id-studiolab/foodSampler/device/hw/foodSampler_v20/_REF/foodSampler_v20_SCHEM.pdf

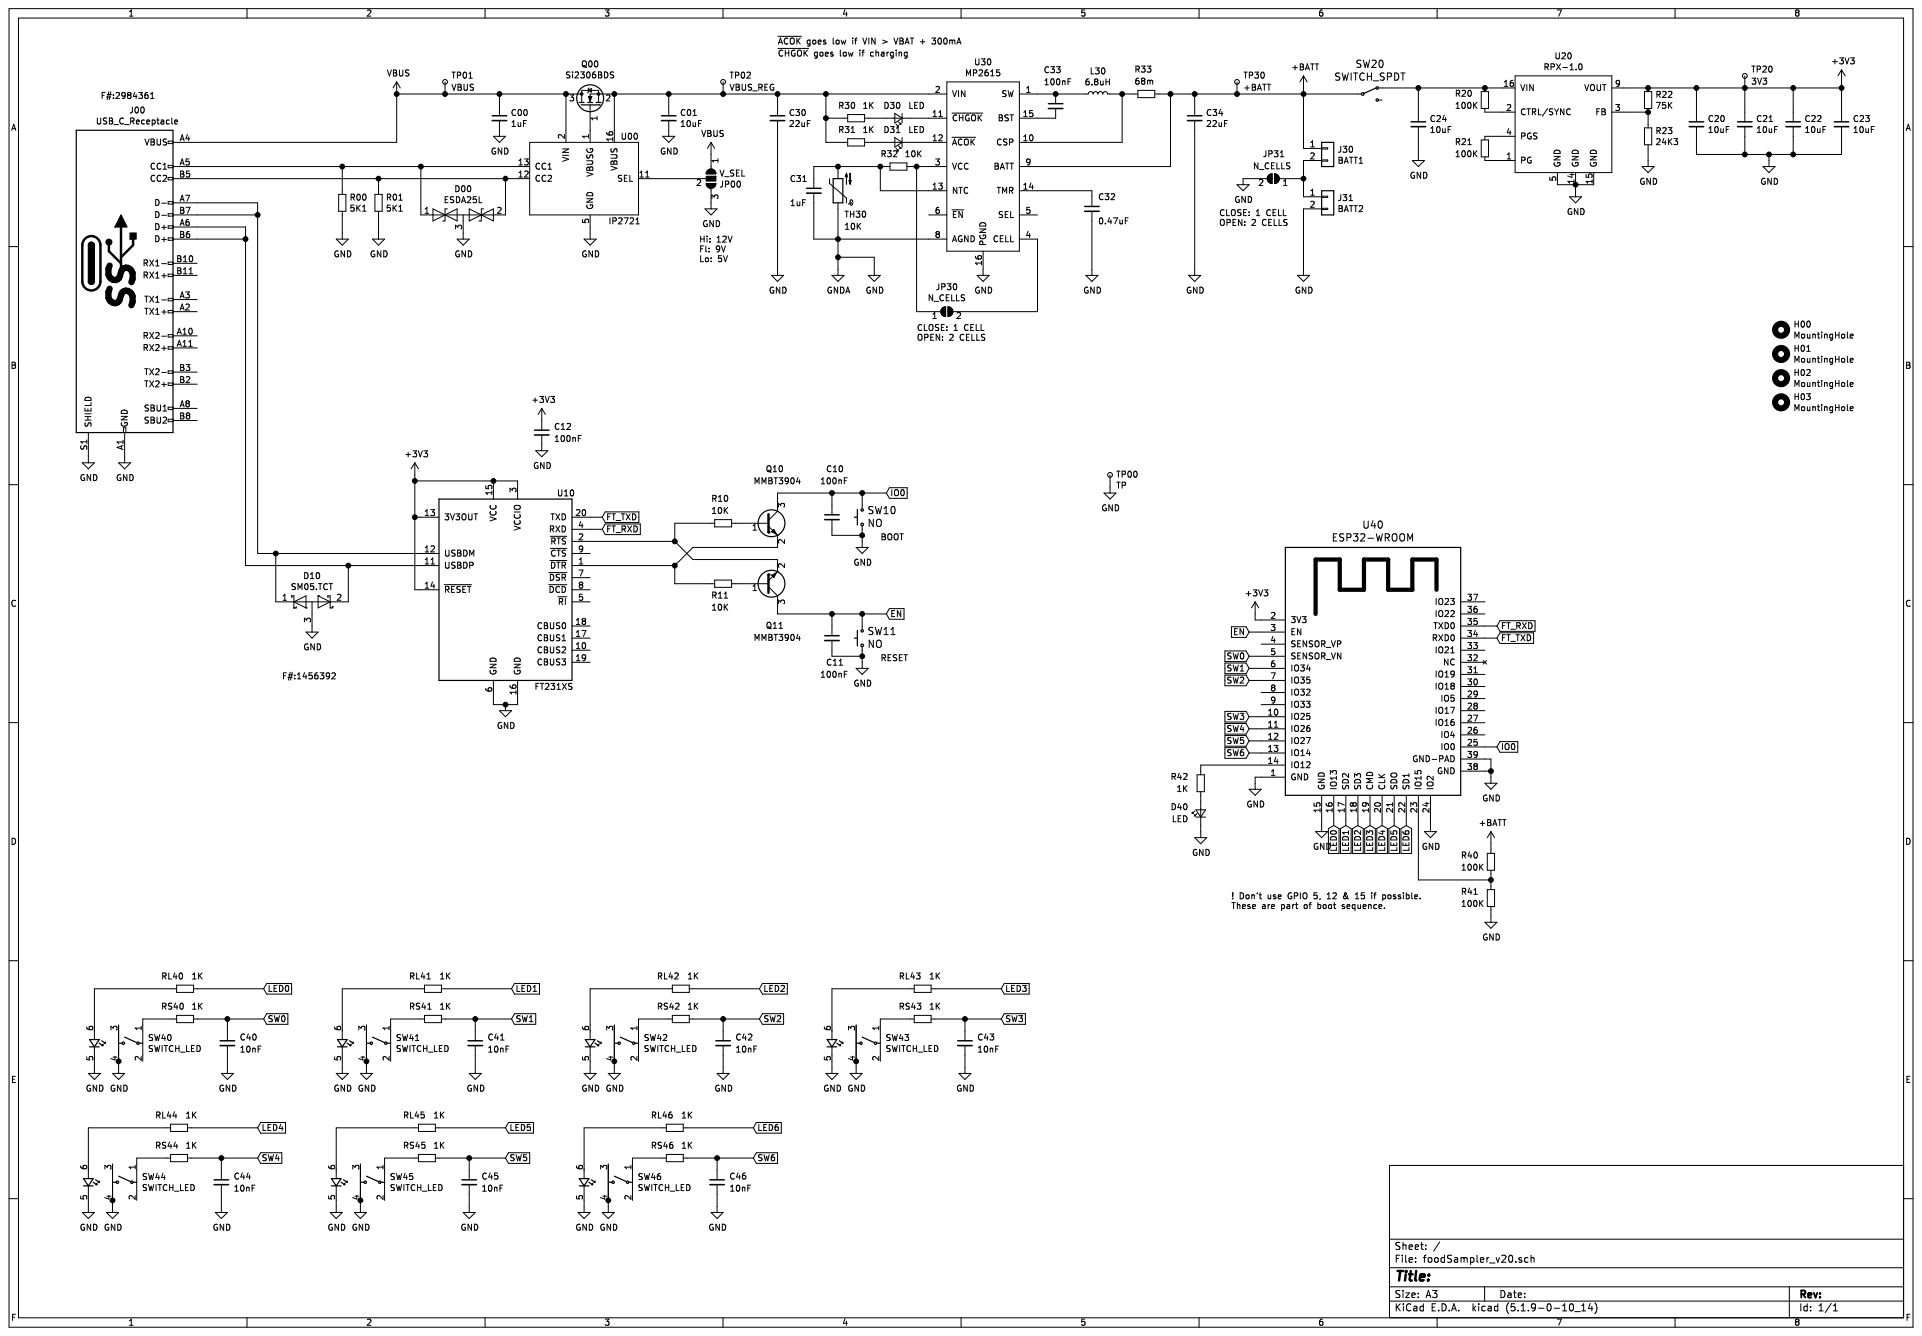
[picture p7: page 1]
