id-studiolab/foodSampler/device/hw/foodSampler_v21/_REF/foodSampler_21-SCHEM.pdf

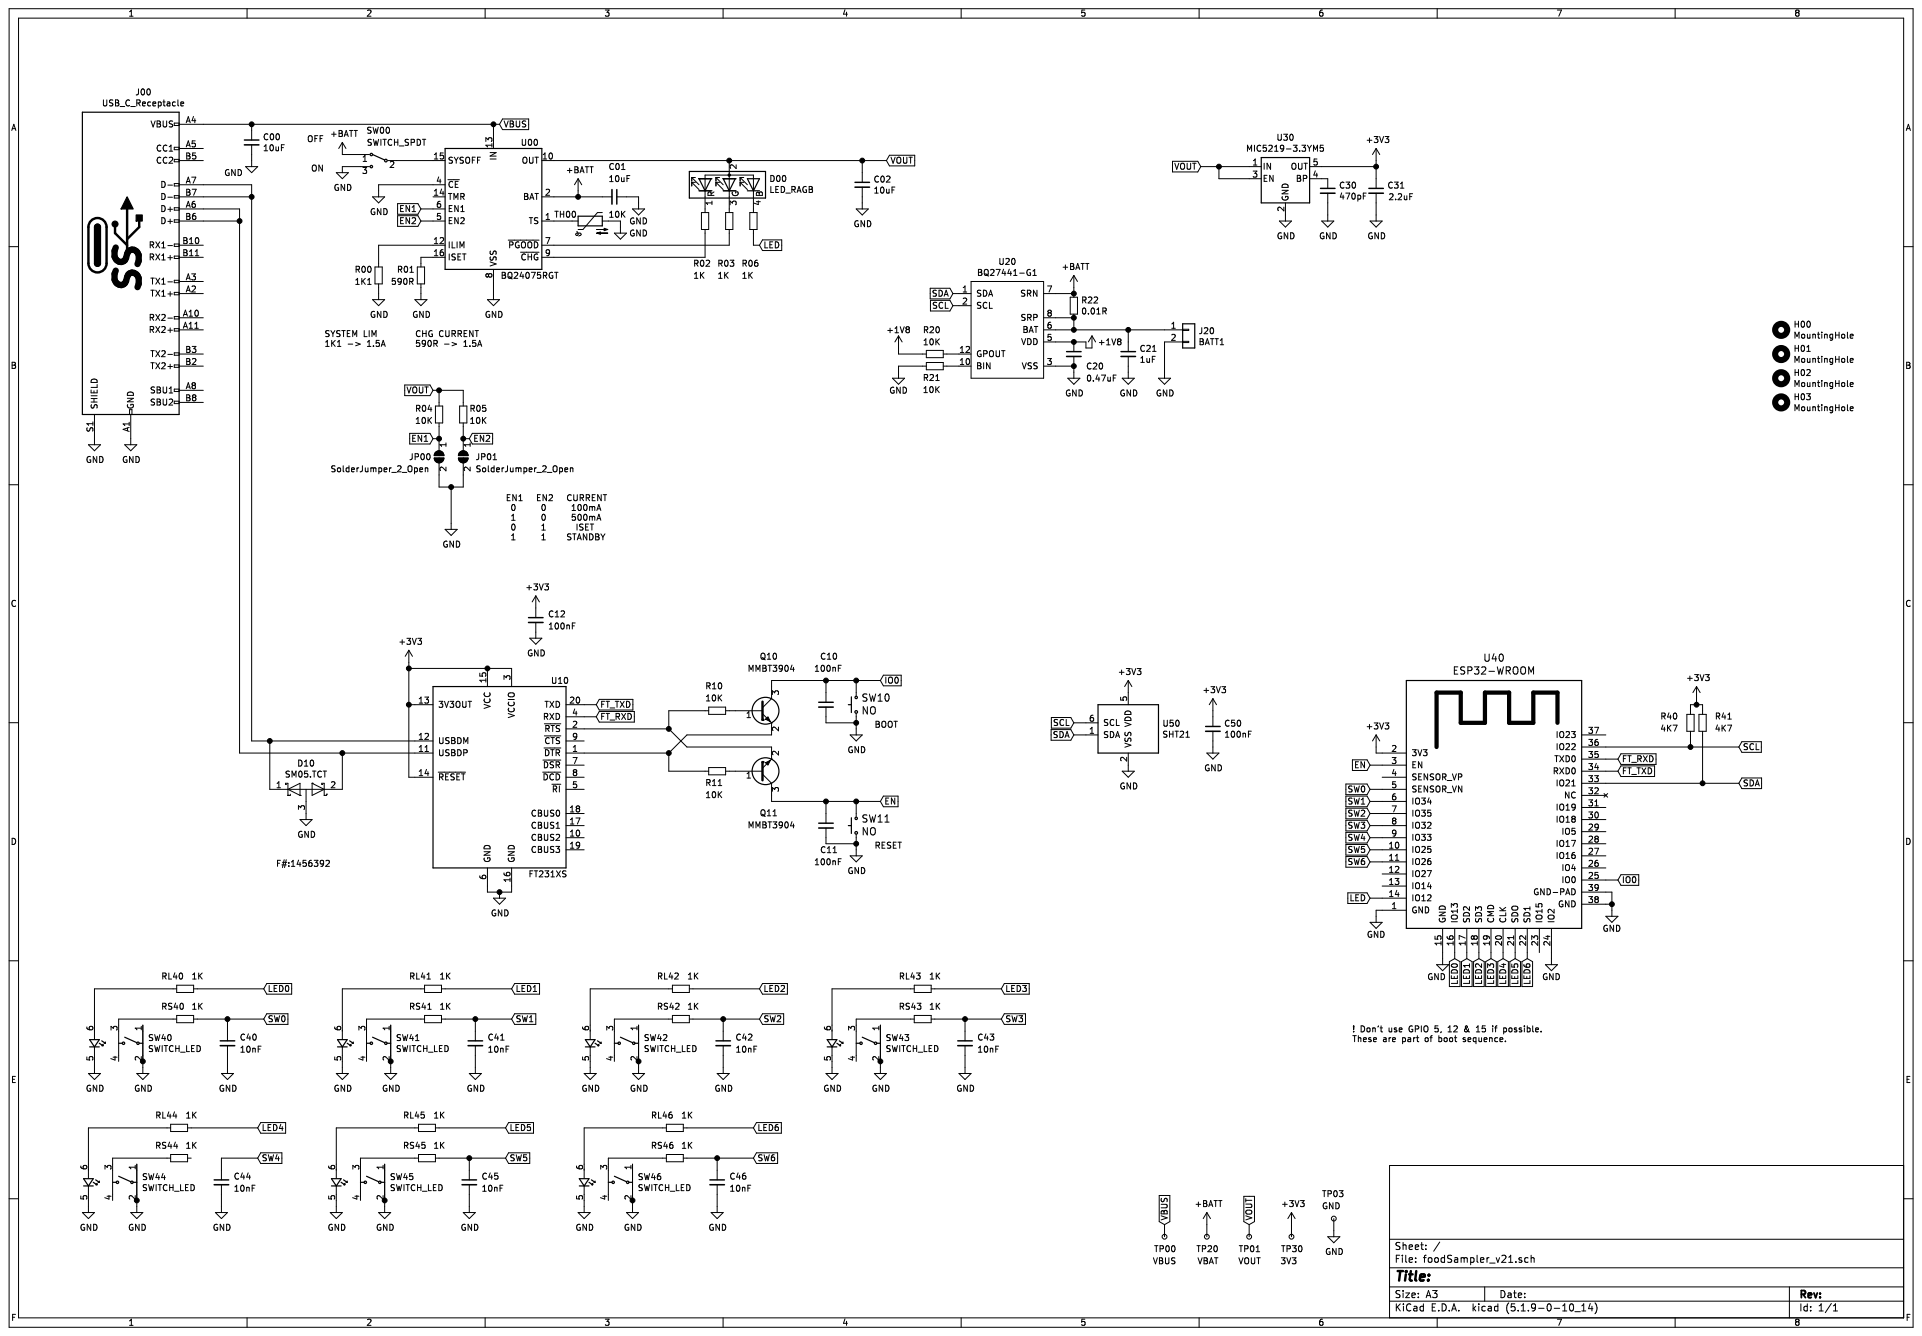
[picture p8: page 1]
