id-studiolab/foodSampler/device/hw/foodSampler_v21/_REF/foodSampler_21-TPLACE.pdf

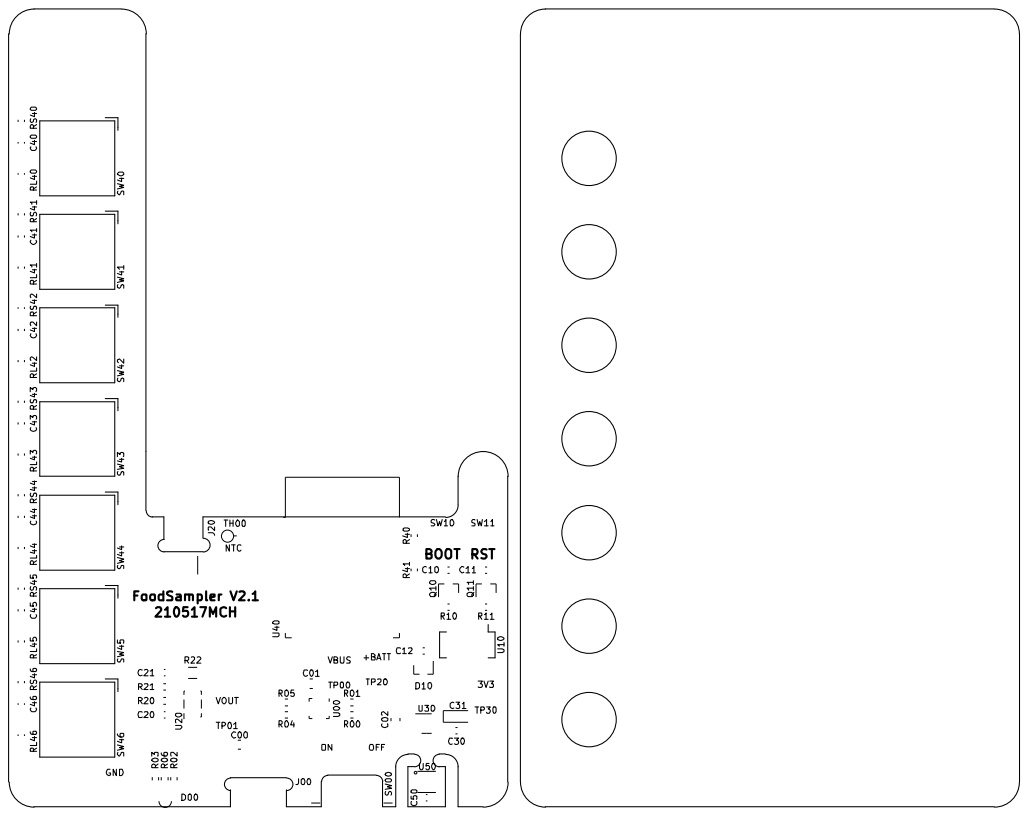
[picture p9: page 1]
