id-studiolab/foodSampler/device/hw/foodSampler_v10/_REF/foodsampler_v10_SCHEM.pdf

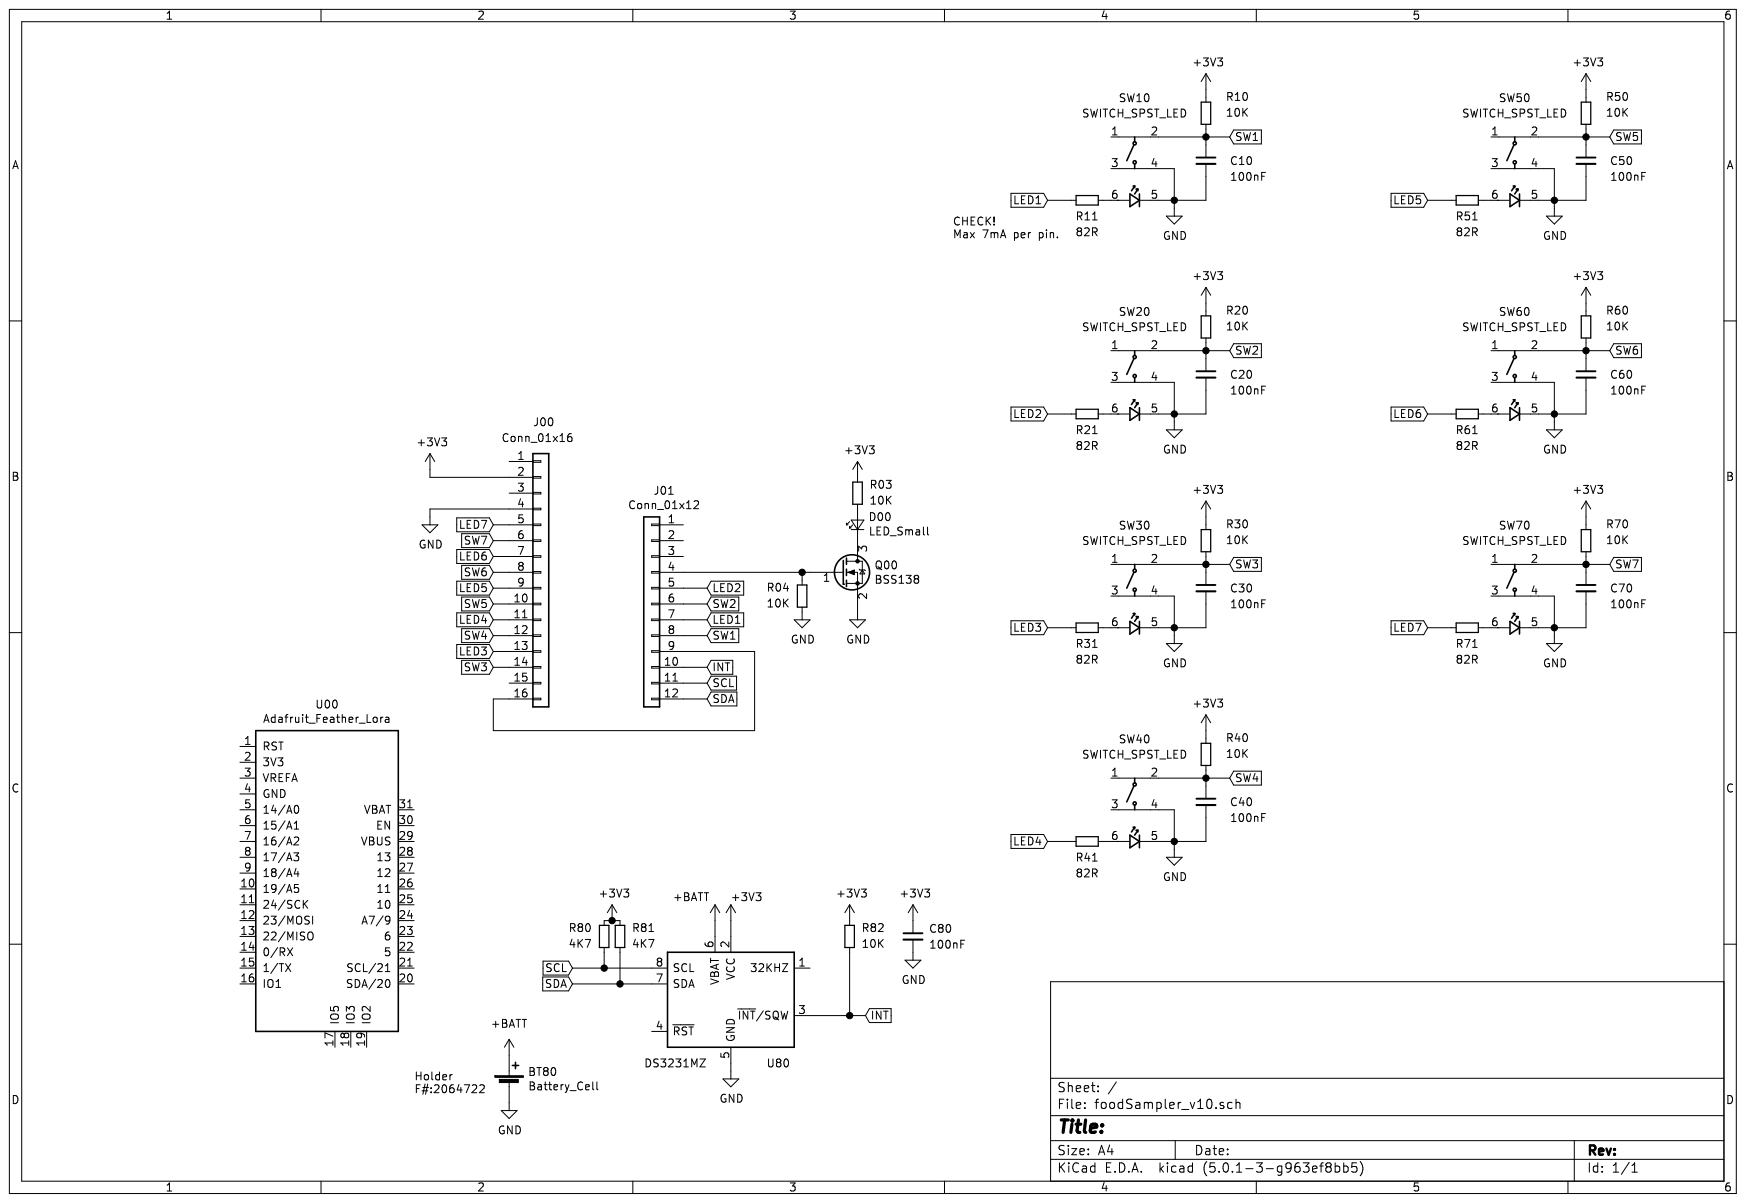
[picture p10: page 1]
