id-studiolab/foodSampler/device/hw/foodSampler_v10/_REF/foodSampler_v10-FRONT.pdf

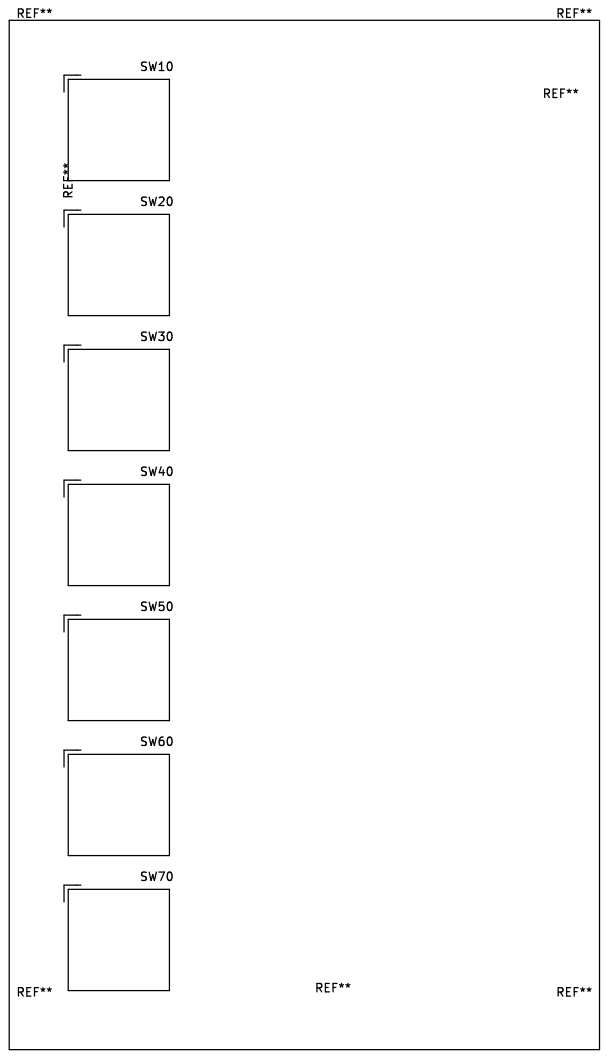
[picture p11: page 1]
