id-studiolab/foodSampler/device/hw/foodSampler_v10/_REF/foodSampler_v10_DIM.pdf

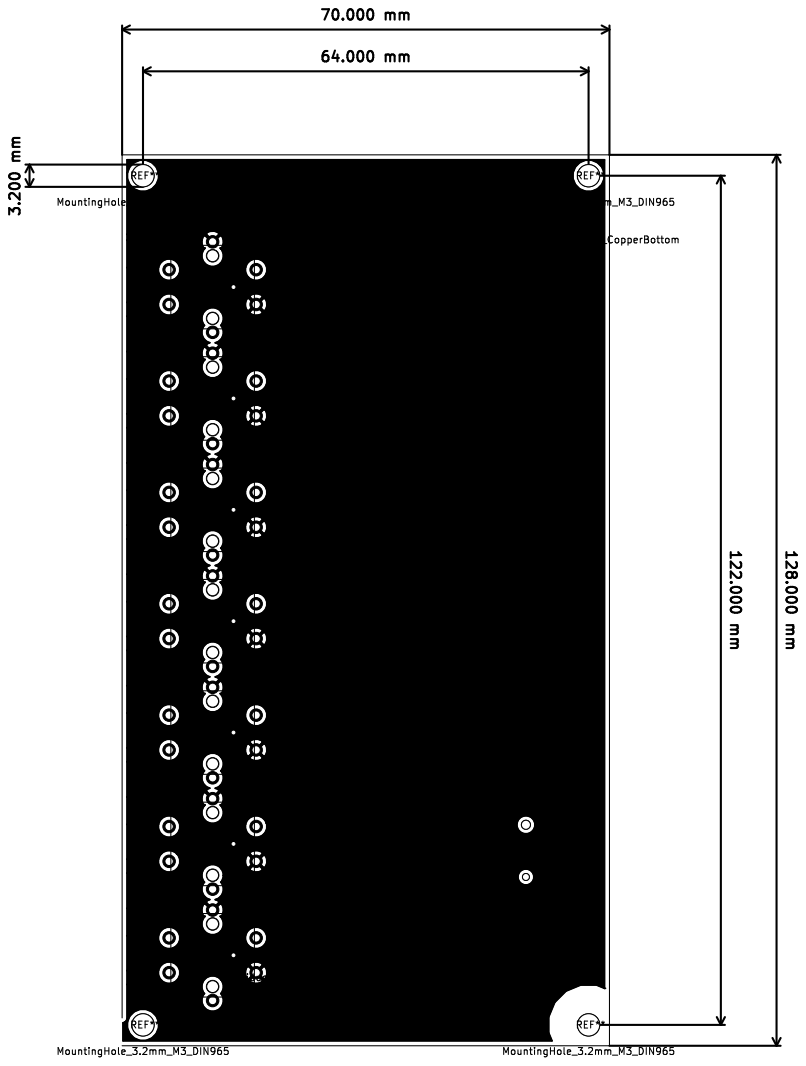
[picture p12: page 1]
