id-studiolab/foodSampler/device/code/foodsampler_v20/auth.h

static const u1_t PROGMEM APPEUI[8]={ 0xB9, 0xAE, 0x01, 0xD0, 0x7E, 0xD5, 0xB3, 0x70 };

static const u1_t DEVEUI_ARRAY[8][8]={
  //making the first blank to be consistent
  { 0x00, 0x00, 0x00, 0x00, 0x00, 0x00, 0x00, 0x00 },
  { 0xD3, 0x07, 0x71, 0x51, 0x18, 0x37, 0x60, 0x00 },
  { 0xD5, 0x07, 0x71, 0x51, 0x18, 0x37, 0x60, 0x00 },
  { 0xD6, 0x07, 0x71, 0x51, 0x18, 0x37, 0x60, 0x00 },
  { 0xD8, 0x07, 0x71, 0x51, 0x18, 0x37, 0x60, 0x00 },
  { 0xD9, 0x07, 0x71, 0x51, 0x18, 0x37, 0x60, 0x00 },
  { 0xDA, 0x07, 0x71, 0x51, 0x18, 0x37, 0x60, 0x00 },
  { 0xDB, 0x07, 0x71, 0x51, 0x18, 0x37, 0x60, 0x00 }
};

static const u1_t PROGMEM APPKEY[16] = { 0x0D, 0x00, 0x02, 0x09, 0x70, 0x5D, 0x06, 0xC0, 0x39, 0x0F, 0x40, 0xEB, 0x04, 0xC0, 0xD6, 0x07 };
