id-studiolab/foodSampler/device/code/test_ttn_device/test_ttn_device.ino

#include <TheThingsNode.h>

// Set your AppEUI and AppKey
const char *appEui = "70B3D57ED001AEB9";
const char *appKey = "A38DCB5F0F0C1A22EF6957C53B7F6D61";

#define loraSerial Serial1
#define debugSerial Serial

// Replace REPLACE_ME with TTN_FP_EU868 or TTN_FP_US915
#define freqPlan TTN_FP_EU868

TheThingsNetwork ttn(loraSerial, debugSerial, freqPlan, 8);
TheThingsNode *node;

#define PORT_SETUP 1
#define PORT_INTERVAL 2
#define PORT_MOTION 3
#define PORT_BUTTON 4

uint8_t btn_id=3;

/*
Decoder payload function
------------------------

function Decoder(bytes, port) {
  var decoded = {};
  var events = {
    1: 'setup',
    2: 'interval',
    3: 'motion',
    4: 'button'
  };
  decoded.event = events[port];
  decoded.battery = (bytes[0] << 8) + bytes[1];
  decoded.light = (bytes[2] << 8) + bytes[3];
  if (bytes[4] & 0x80)
    decoded.temperature = ((0xffff << 16) + (bytes[4] << 8) + bytes[5]) / 100;
  else
    decoded.temperature = ((bytes[4] << 8) + bytes[5]) / 100;
  return decoded;
}
*/

void setup()
{
  loraSerial.begin(57600);
  debugSerial.begin(9600);

  // Wait a maximum of 10s for Serial Monitor
  while (!debugSerial && millis() < 10000)
    ;

  // Config Node
  node = TheThingsNode::setup();
  node->configLight(true);
  node->configInterval(true, 60000);
  node->configTemperature(true);
  node->onWake(wake);
  node->onInterval(interval);
  node->onSleep(sleep);
  node->onMotionStart(onMotionStart);
  node->onButtonRelease(onButtonRelease);

  // Test sensors and set LED to GREEN if it works
  node->showStatus();
  node->setColor(TTN_GREEN);

  debugSerial.println("-- TTN: STATUS");
  ttn.showStatus();

  debugSerial.println("-- TTN: JOIN");
  ttn.join(appEui, appKey);

  debugSerial.println("-- SEND: SETUP");
  sendData(PORT_SETUP);
}

void loop()
{
  node->loop();
}

void interval()
{
  node->setColor(TTN_BLUE);

  debugSerial.println("-- SEND: INTERVAL");
  sendData(PORT_INTERVAL);
}

void wake()
{
  node->setColor(TTN_GREEN);
    // Config Node
  node->showStatus();
}

void sleep()
{
  node->setColor(TTN_BLACK);
}

void onMotionStart()
{
  node->setColor(TTN_BLUE);

  debugSerial.print("-- SEND: MOTION");
  sendData(PORT_MOTION);
}

void onButtonRelease(unsigned long duration)
{
  node->setColor(TTN_BLUE);

  debugSerial.print("-- SEND: BUTTON");
  debugSerial.println(duration);

  sendData(PORT_BUTTON);
}

void sendData(uint8_t port){
  // Wake RN2483
  ttn.wake();

  ttn.showStatus();
  node->showStatus();

  byte *bytes;
  byte payload[3];

  uint16_t battery = node->getBattery();
  bytes = (byte *)&battery;
  payload[0] = bytes[0];
  payload[1] = bytes[1];

  payload[2] = btn_id;
  
  ttn.sendBytes(payload, sizeof(payload), port);

  // Set RN2483 to sleep mode
  ttn.sleep(60000);

  // This one is not optionnal, remove it
  // and say bye bye to RN2983 sleep mode
  delay(500);
}
